harbaum/fischertechnik-joystick/images/device_manager.png

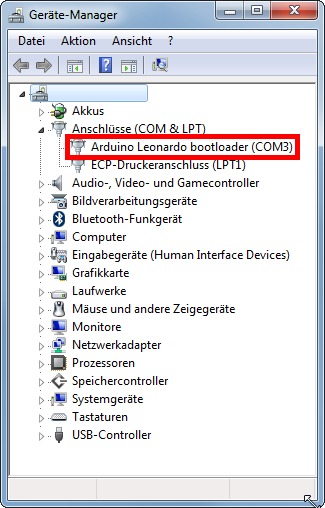
images/device_manager.png
